ulrichard/homeauto/static/B_0.png

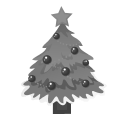
static/B_0.png
